wormyrocks/super_otamatone/arduino/otamatone/MenuSystem.cpp

/*
   Copyright (c) 2015, 2016 arduino-menusystem
   Licensed under the MIT license (see LICENSE)
*/

#include "MenuSystem.h"
#include <stdlib.h>


// *********************************************************
// MenuComponent
// *********************************************************

MenuComponent::MenuComponent(const char* name)
  : _name(name),
    _has_focus(false),
    _is_current(false)
{
}

const char* MenuComponent::get_name() const
{
  return _name;
}

void MenuComponent::set_name(const char* name)
{
  _name = name;
}

bool MenuComponent::has_focus() const
{
  return _has_focus;
}

bool MenuComponent::is_current() const
{
  return _is_current;
}

void MenuComponent::set_current(bool is_current)
{
  _is_current = is_current;
}



// *********************************************************
// Menu
// *********************************************************

Menu::Menu(const char* name)
  : MenuComponent(name),
    _p_current_component(nullptr),
    _menu_components(nullptr),
    _p_parent(nullptr),
    _select_fn(nullptr),
    _num_components(0),
    _current_component_num(0),
    _previous_component_num(0)
{
}

bool Menu::next(bool loop)
{
  _previous_component_num = _current_component_num;

  if (!_num_components)
  {
    return false;
  }
  else if (_current_component_num != _num_components - 1)
  {
    _current_component_num++;
    _p_current_component = _menu_components[_current_component_num];

    _p_current_component->set_current();
    _menu_components[_previous_component_num]->set_current(false);
    return true;
  }
  else if (loop)
  {
    _current_component_num = 0;
    _p_current_component = _menu_components[_current_component_num];

    _p_current_component->set_current();
    _menu_components[_previous_component_num]->set_current(false);

    return true;
  }
  return false;
}

bool Menu::prev(bool loop)
{
  _previous_component_num = _current_component_num;

  if (!_num_components)
  {
    return false;
  }
  else if (_current_component_num != 0)
  {
    _current_component_num--;
    _p_current_component = _menu_components[_current_component_num];

    _p_current_component->set_current();
    _menu_components[_previous_component_num]->set_current(false);

    return true;
  }
  else if (loop)
  {
    _current_component_num = _num_components - 1;
    _p_current_component = _menu_components[_current_component_num];

    _p_current_component->set_current();
    _menu_components[_previous_component_num]->set_current(false);

    return true;
  }
  return false;
}

Menu* Menu::activate()
{
  if (!_num_components)
    return nullptr;

  MenuComponent* pComponent = _menu_components[_current_component_num];

  if (pComponent == nullptr)
    return nullptr;

  return pComponent->select();
}

void Menu::set_select_function(SelectFnPtr select_fn)
{
  _select_fn = select_fn;
}

Menu* Menu::select()
{
  return this;
}

void Menu::reset()
{
  for (int i = 0; i < _num_components; ++i)
    _menu_components[i]->reset();

  _p_current_component->set_current(false);
  _previous_component_num = 0;
  _current_component_num = 0;
  _p_current_component = _num_components ? _menu_components[0] : nullptr;
  _p_current_component->set_current();
}

void Menu::add_item(MenuItem* pItem)
{
  // Resize menu component list, keeping existing items.
  // If it fails, there the item is not added and the function returns.
  _menu_components = (MenuComponent**) realloc(_menu_components,
                     (_num_components + 1)
                     * sizeof(MenuComponent*));
  if (_menu_components == nullptr)
    return;

  _menu_components[_num_components] = pItem;

  if (_num_components == 0)
  {
    _p_current_component = pItem;
    _p_current_component->set_current();
  }

  _num_components++;
}

void Menu::hide_n_items(uint8_t n) {
  _num_components -= n;
}

void Menu::show_n_items(uint8_t n) {
  _num_components += n;
}

Menu const* Menu::get_parent() const
{
  return _p_parent;
}

void Menu::set_parent(Menu* pParent)
{
  _p_parent = pParent;
}

void Menu::add_menu(Menu* pMenu)
{
  // Resize menu component list, keeping existing items.
  // If it fails, there the item is not added and the function returns.
  _menu_components = (MenuComponent**) realloc(_menu_components,
                     (_num_components + 1)
                     * sizeof(MenuComponent*));
  if (_menu_components == nullptr)
    return;

  pMenu->set_parent(this);

  _menu_components[_num_components] = pMenu;

  if (_num_components == 0)
  {
    _p_current_component = pMenu;
    _p_current_component->set_current();
  }

  _num_components++;
}

MenuComponent const* Menu::get_menu_component(uint8_t index) const
{
  return _menu_components[index];
}

MenuComponent const* Menu::get_current_component() const
{
  return _p_current_component;
}

uint8_t Menu::get_num_components() const
{
  return _num_components;
}

uint8_t Menu::get_current_component_num() const
{
  return _current_component_num;
}

uint8_t Menu::get_previous_component_num() const
{
  return _previous_component_num;
}

void Menu::render(MenuComponentRenderer const& renderer) const
{
  renderer.render_menu(*this);
}

void Menu::fs_render(MenuComponentRenderer const& renderer) const
{
  renderer.fs_menu_render(*this);
}

// *********************************************************
// BigNumberComponent
// *********************************************************

BigNumberSlider::BigNumberSlider(const char* name,
                                 uint8_t value, uint8_t minValue, uint8_t maxValue,
                                 uint8_t increment, uint8_t animation, SelectFnPtr select_fn)
  : Menu(name),
    _value(value),
    _minValue(minValue),
    _maxValue(maxValue),
    _increment(increment),
    _animation(animation)

{
  set_select_function(select_fn);
  _slider_divs = (maxValue - minValue) / increment;
};

Menu* BigNumberSlider::select()
{
  _has_focus = !_has_focus;
  // Only run _select_fn when the user is done editing the value
  if (!_has_focus && _select_fn != nullptr)
    _select_fn(this);
  return nullptr;
}

void BigNumberSlider::render(MenuComponentRenderer const& renderer) const
{
  renderer.render_big_number_item(*this);
}
void BigNumberSlider::fs_render(MenuComponentRenderer const& renderer) const
{
  renderer.fs_bignumber_render(*this);
}
uint8_t BigNumberSlider::get_value() const
{
  return _value;
}

uint8_t BigNumberSlider::get_minValue() const
{
  return _minValue;
}

uint8_t BigNumberSlider::get_maxValue() const
{
  return _maxValue;
}

void BigNumberSlider::set_value(uint8_t value)
{
  _value = value;
}

void BigNumberSlider::set_min_value(uint8_t value)
{
  _minValue = value;
}

void BigNumberSlider::set_max_value(uint8_t value)
{
  _maxValue = value;
}

bool BigNumberSlider::next(bool loop)
{
  _value += _increment;
  if (_value > _maxValue)
  {
    if (loop)
      _value = _minValue;
    else
      _value = _maxValue;
  }
  return true;
}

bool BigNumberSlider::prev(bool loop)
{
  _value -= _increment;
  if (_value < _minValue)
  {
    if (loop)
      _value = _maxValue;
    else
      _value = _minValue;
  }
  return true;
}

uint8_t BigNumberSlider::get_current_component_num() const
{
  return _value;
}

uint8_t BigNumberSlider::get_num_components() const
{
  return _slider_divs;
}

uint8_t BigNumberSlider::get_animation() const {
  return _animation;
}

// *********************************************************
// BackMenuItem
// *********************************************************

BackMenuItem::BackMenuItem(const char* name, SelectFnPtr select_fn,
                           MenuSystem* ms)
  : MenuItem(name, select_fn),
    menu_system(ms)
{
}

Menu* BackMenuItem::select()
{
  if (_select_fn != nullptr)
    _select_fn(this);

  if (menu_system != nullptr)
    menu_system->back();

  return nullptr;
}

void BackMenuItem::render(MenuComponentRenderer const& renderer) const
{
  renderer.render_back_menu_item(*this);
}

// *********************************************************
// MenuItem
// *********************************************************

MenuItem::MenuItem(const char* name, SelectFnPtr select_fn)
  : MenuComponent(name),
    _select_fn(select_fn)
{
}

void MenuItem::set_select_function(SelectFnPtr select_fn)
{
  _select_fn = select_fn;
}

Menu* MenuItem::select()
{
  if (_select_fn != nullptr)
    _select_fn(this);

  return nullptr;
}

void MenuItem::reset()
{
  // Do nothing.
}

void MenuItem::render(MenuComponentRenderer const& renderer) const
{
  renderer.render_menu_item(*this);
}

bool MenuItem::next(bool loop)
{
  return false;
}

bool MenuItem::prev(bool loop)
{
  return false;
}

// *********************************************************
// NumericMenuItem
// *********************************************************

NumericMenuItem::NumericMenuItem(const char* basename, SelectFnPtr select_fn,
                                 float value, float minValue, float maxValue,
                                 float increment,
                                 FormatValueFnPtr format_value_fn)
  : MenuItem(basename, select_fn),
    _value(value),
    _minValue(minValue),
    _maxValue(maxValue),
    _increment(increment),
    _format_value_fn(format_value_fn)
{
  if (_increment < 0.0) _increment = -_increment;
  if (_minValue > _maxValue)
  {
    float tmp = _maxValue;
    _maxValue = _minValue;
    _minValue = tmp;
  }
};

void NumericMenuItem::set_number_formatter(FormatValueFnPtr format_value_fn)
{
  _format_value_fn = format_value_fn;
}

Menu* NumericMenuItem::select()
{
  _has_focus = !_has_focus;

  // Only run _select_fn when the user is done editing the value
  if (!_has_focus && _select_fn != nullptr)
    _select_fn(this);
  return nullptr;
}

void NumericMenuItem::render(MenuComponentRenderer const& renderer) const
{
  renderer.render_numeric_menu_item(*this);
}

float NumericMenuItem::get_value() const
{
  return _value;
}

float NumericMenuItem::get_minValue() const
{
  return _minValue;
}

float NumericMenuItem::get_maxValue() const
{
  return _maxValue;
}

String NumericMenuItem::get_value_string() const
{
  String buffer;
  if (_format_value_fn != nullptr)
    buffer += _format_value_fn(_value);
  else
    buffer += _value;
  return buffer;
}

void NumericMenuItem::set_value(float value)
{
  _value = value;
}

void NumericMenuItem::set_min_value(float value)
{
  _minValue = value;
}

void NumericMenuItem::set_max_value(float value)
{
  _maxValue = value;
}

bool NumericMenuItem::next(bool loop)
{
  _value += _increment;
  if (_value > _maxValue)
  {
    if (loop)
      _value = _minValue;
    else
      _value = _maxValue;
  }
  return true;
}

bool NumericMenuItem::prev(bool loop)
{
  _value -= _increment;
  if (_value < _minValue)
  {
    if (loop)
      _value = _maxValue;
    else
      _value = _minValue;
  }
  return true;
}


// *********************************************************
// MenuSystem
// *********************************************************

MenuSystem::MenuSystem(MenuComponentRenderer const& renderer)
  : _p_root_menu(new Menu("")),
    _p_curr_menu(_p_root_menu),
    _renderer(renderer)
{
}

bool MenuSystem::next(bool loop)
{
  if (_p_curr_menu->_p_current_component == nullptr) return _p_curr_menu->next(loop);
  if (_p_curr_menu->_p_current_component->has_focus())
    return _p_curr_menu->_p_current_component->next(loop);
  else
    return _p_curr_menu->next(loop);
}

bool MenuSystem::prev(bool loop)
{
  if (_p_curr_menu->_p_current_component == nullptr) return _p_curr_menu->prev(loop);
  if (_p_curr_menu->_p_current_component->has_focus())
    return _p_curr_menu->_p_current_component->prev(loop);
  else
    return _p_curr_menu->prev(loop);
}

void MenuSystem::reset()
{
  _p_curr_menu = _p_root_menu;
  _p_root_menu->reset();
}

void MenuSystem::select(bool reset)
{
  Menu* pMenu = _p_curr_menu->activate();

  if (pMenu != nullptr)
    _p_curr_menu = pMenu;
  else if (reset)
    this->reset();
}

bool MenuSystem::back()
{
  if (_p_curr_menu->_select_fn != nullptr){
    _p_curr_menu->_select_fn(_p_curr_menu);
  }

  if (_p_curr_menu != _p_root_menu)
  {
    _p_curr_menu = const_cast<Menu*>(_p_curr_menu->get_parent());
    return true;
  }
  // We are already in the root menu
  return false;
}

Menu& MenuSystem::get_root_menu() const
{
  return *_p_root_menu;
}

Menu const* MenuSystem::get_current_menu() const
{
  return _p_curr_menu;
}

void MenuSystem::display() const
{
  if (_p_curr_menu != nullptr)
    _renderer.render(*_p_curr_menu);
}
