wormyrocks/super_otamatone/arduino/otamatone/MenuSystem.h

/*
   Copyright (c) 2015, 2016 arduino-menusystem
   Licensed under the MIT license (see LICENSE)
*/

#ifndef MENUSYSTEM_H
#define MENUSYSTEM_H

#if defined(ARDUINO) && ARDUINO >= 100
#include <Arduino.h>
#else
#include <WProgram.h>
#endif

class Menu;
class MenuComponentRenderer;
class MenuSystem;

//! \brief Abstract base class that represents a component in the menu
//!
//! This is the abstract base class for the main components used to build a
//! menu structure: Menu and MenuItem.
//!
//! MenuComponent should not be used as a base class in clients. Instead use
//! either Menu or MenuItem.
//!
//! MenuComponent is the `Component` part of the composite design pattern (see:
//! https://en.wikipedia.org/wiki/Composite_pattern).
//!
//! \see Menu
//! \see MenuItem
class MenuComponent
{
    friend class MenuSystem;
    friend class Menu;
  public:
    //! \brief Construct a MenuComponent
    //! \param[in] name The name of the menu component that is displayed in
    //!                 clients.
    MenuComponent(const char* name);

    //! \brief Set the component's name
    //! \param[in] name The name of the menu component that is displayed in
    //!                 clients.
    void set_name(const char* name);

    //! \brief Gets the component's name
    //! \returns The component's name.
    const char* get_name() const;

    //! \brief Renders the component using the given MenuComponentRenderer
    //!
    //! This is the `accept` method in the visitor design pattern. It should
    //! call the appropriate method on the given MenuComponentRenderer for
    //! rendering this type of component. This method should be called from the
    //! MenuComponent::render method.
    //!
    //! \param[in] renderer The MenuComponentRenderer to use to render this
    //!                     component
    //!
    //! \see MenuComponentRenderer
    virtual void render(MenuComponentRenderer const& renderer) const = 0;
    //! \brief Returns true if this component has focus; false otherwise
    //!
    //! A component has focus when the next and prev functions are able to
    //! change its state rather than navigate the menu structure. It's
    //! primarily used in NumericMenuItem so next and prev change the value
    //! associated with the component.
    //!
    //! Subclasses should set _has_focus to true when this behaviour is desired
    //! and reset it to false when it's no longer required. The usual place to
    //! do this is in the MenuComponent::select method.
    //!
    //! \returns true if this component has focus, false otherwise.
    //!
    //! \see MenuComponent::select
    //! \see NumericMenuComponent
    bool has_focus() const;

    //! \brief Returns true if this is the current component; false otherwise
    //!
    //! This bool registers if the component is the current selected component.
    //!
    //! Subclasses should use set_current() when the component becomes
    //! activated and use set_previous() once the component is no longer the
    //! current component.
    //!
    //! \returns true if this component is the current component, false
    //!          otherwise.
    //! \see MenuComponent::set_current
    bool is_current() const;

  protected:
    //! \brief Processes the next action
    //!
    //! The behaviour of this function can differ depending on whether
    //! MenuComponent::has_focus returns true or false.
    //!
    //! When MenuComponent::has_focus returns true, this method should change
    //! some state in the component; when it returns false, this method should
    //! navigate the menu structure.
    //!
    //! \param[in] loop if true the action should loop around to the beginning
    //!                 for finite ranges; otherwise overflow should be
    //!                 prevented.
    //! \returns true if the component processed the action, false otherwise.
    //!
    //! \see MenuComponent::prev
    //! \see MenuComponent::has_focus
    virtual bool next(bool loop = false) = 0;

    //! \brief Processes the prev action
    //!
    //! The behaviour of this function can differ depending on whether
    //! MenuComponent::has_focus returns true or false.
    //!
    //! When MenuComponent::has_focus returns true, this method should change
    //! some state in the component; when it returns false, this method should
    //! navigate the menu structure.
    //!
    //! \param[in] loop if true the action should loop around to the end
    //!                 for finite ranges; otherwise overflow should be
    //!                 prevented.
    //! \returns true if the component processed the action, false otherwise.
    //!
    //! \see MenuComponent::next
    //! \see MenuComponent::has_focus
    virtual bool prev(bool loop = false) = 0;

    //! \brief Resets the component to its initial state
    virtual void reset() = 0;

    //! \brief Processes the select action
    //!
    //! When a menu component is selected by the client an action may need to
    //! performed.
    //!
    //! If the component supports focus, this method is the recommended place
    //! set _has_focus to true so the MenuComponent::next and
    //! MenuComponent::prev methods can be used to change some state in the
    //! component.
    //!
    //! \returns The Menu instance selected or nullptr. The returned Menu
    //!          instance is used in MenuSystem::activate to set the current
    //!          menu in the MenuSystem.
    //!
    //! \see MenuComponent::has_focus
    //! \see NumericMenuComponent
    virtual Menu* select() = 0;

    //! \brief Set the current state of the component
    //!
    //! \paran is_current true if this component is the current one; false
    //!                   otherwise.
    //! \see is_current
    void set_current(bool is_current = true);

  protected:
    const char* _name;
    bool _has_focus;
    bool _is_current;
};


//! \brief A MenuComponent that calls a callback function when selected.
//!
//! MenuItem represents the `Leaf` in the composite design pattern (see:
//! https://en.wikipedia.org/wiki/Composite_pattern). When a MenuItem is
//! selected, the user-defined MenuItem::_select_fn callback is called.
//!
//! \see MenuComponent
//! \see Menu
class MenuItem : public MenuComponent
{
  public:
    //! \brief Callback for when the MenuItem is selected
    //!
    //! \param menu_item The menu item being selected.
    using SelectFnPtr = void (*)(MenuItem* menu_item);

  public:
    //! \brief Construct a MenuItem
    //! \param[in] name The name of the menu component that is displayed in
    //!                 clients.
    //! \param[in] select_fn The function to call when the MenuItem is
    //!                      selected.
    MenuItem(const char* name, SelectFnPtr select_fn);

    //! \brief Sets the function to call when the MenuItem is selected
    //! \param[in] select_fn The function to call when the MenuItem is
    //!                      selected.
    void set_select_function(SelectFnPtr select_fn);

    //! \copydoc MenuComponent::render
    virtual void render(MenuComponentRenderer const& renderer) const;

  protected:
    //! \copydoc MenuComponent::next
    //!
    //! This method does nothing in MenyItem.
    virtual bool next(bool loop = false);

    //! \copydoc MenuComponent::prev
    //!
    //! This method does nothing in MenuItem.
    virtual bool prev(bool loop = false);

    //! \copydoc MenuComponent::reset
    //!
    //! This method does nothing in MenuItem.
    virtual void reset();

    //! \copydoc MenuComponent:select
    virtual Menu* select();

  protected:
    SelectFnPtr _select_fn;
};

//! \brief A MenuItem that calls MenuSystem::back() when selected.
//! \see MenuItem
class BackMenuItem : public MenuItem
{
  public:
    BackMenuItem(const char* name, SelectFnPtr select_fn, MenuSystem* ms);

    virtual void render(MenuComponentRenderer const& renderer) const;

  protected:
    virtual Menu* select();

  protected:
    MenuSystem* menu_system;
};


class NumericMenuItem : public MenuItem
{
  public:
    //! \brief Callback for formatting the numeric value into a String.
    //!
    //! \param value The value to convert.
    //! \returns The String representation of value.
    using FormatValueFnPtr = const String (*)(const float value);

  public:
    /// Constructor
    ///
    /// @param name The name of the menu item.
    /// @param select_fn The function to call when this MenuItem is selected.
    /// @param value Default value.
    /// @param minValue The minimum value.
    /// @param maxValue The maximum value.
    /// @param increment How much the value should be incremented by.
    /// @param valueFormatter The custom formatter. If nullptr the String float
    ///                       formatter will be used.
    NumericMenuItem(const char* name, SelectFnPtr select_fn,
                    float value, float minValue, float maxValue,
                    float increment = 1.0,
                    FormatValueFnPtr format_value_fn = nullptr);

    /**
       Sets the custom number formatter.

       @param numberFormat the custom formatter. If nullptr the String float
                           formatter will be used (2 decimals)
    */
    void set_number_formatter(FormatValueFnPtr format_value_fn);

    float get_value() const;
    float get_minValue() const;
    float get_maxValue() const;

    // TODO: get_value_string is a poor name. get_formatted_value maybe?
    String get_value_string() const;
    void set_value(float value);
    void set_min_value(float value);
    void set_max_value(float value);

    virtual void render(MenuComponentRenderer const& renderer) const;

  protected:
    virtual bool next(bool loop = false);
    virtual bool prev(bool loop = false);

    virtual Menu* select();

  protected:
    float _value;
    float _minValue;
    float _maxValue;
    float _increment;
    FormatValueFnPtr _format_value_fn;
};


class Menu : public MenuComponent
{
    friend class MenuSystem;
  public:
    using SelectFnPtr = void (*)(Menu *menu);

    Menu(const char* name);

    void add_item(MenuItem* pItem);
    void add_menu(Menu* pMenu);
    void hide_n_items(uint8_t n);
    void show_n_items(uint8_t n);

    MenuComponent const* get_current_component() const;
    MenuComponent const* get_menu_component(uint8_t index) const;

    virtual uint8_t get_num_components() const;
    virtual uint8_t get_current_component_num() const;
    virtual uint8_t get_previous_component_num() const;

    virtual void render(MenuComponentRenderer const& renderer) const;
    virtual void fs_render(MenuComponentRenderer const& renderer) const;
  protected:
    void set_parent(Menu* pParent);
    Menu const* get_parent() const;

    Menu* activate();
    virtual bool next(bool loop = false);
    virtual bool prev(bool loop = false);
    virtual Menu* select();
    virtual void reset();
    void set_select_function(SelectFnPtr select_fn);
    SelectFnPtr _select_fn;

  private:
    MenuComponent* _p_current_component;
    MenuComponent** _menu_components;
    Menu* _p_parent;
    uint8_t _num_components;
    uint8_t _current_component_num;
    uint8_t _previous_component_num;
};

class BigNumberSlider : public Menu
{
  public:

    BigNumberSlider(const char* name,
                    uint8_t value, uint8_t minValue, uint8_t maxValue,
                    uint8_t increment, uint8_t animation, SelectFnPtr select_fn);


    uint8_t get_value() const;
    uint8_t get_minValue() const;
    uint8_t get_maxValue() const;
    uint8_t get_animation() const;
    uint8_t get_num_components() const;
    uint8_t get_current_component_num() const;

    void set_value(uint8_t value);
    void set_min_value(uint8_t value);
    void set_max_value(uint8_t value);
    virtual void render(MenuComponentRenderer const& renderer) const;
    virtual void fs_render(MenuComponentRenderer const& renderer) const;

  protected:
    virtual bool next(bool loop = false);
    virtual bool prev(bool loop = false);
    virtual Menu* select();

  private:
    uint8_t _value;
    uint8_t _animation;
    uint8_t _minValue;
    uint8_t _maxValue;
    uint8_t _increment;
    uint8_t _slider_divs;

};


class MenuSystem
{
  public:
    MenuSystem(MenuComponentRenderer const& renderer);

    void display() const;
    bool next(bool loop = false);
    bool prev(bool loop = false);
    void reset();
    void select(bool reset = false);
    bool back();

    Menu& get_root_menu() const;
    Menu const* get_current_menu() const;

  private:
    Menu* _p_root_menu;
    Menu* _p_curr_menu;
    MenuComponentRenderer const& _renderer;
};


class MenuComponentRenderer
{
  public:
    virtual void render(Menu const& menu) const = 0;
    virtual void render_menu_item(MenuItem const& menu_item) const = 0;
    virtual void render_back_menu_item(BackMenuItem const& menu_item) const = 0;
    virtual void render_numeric_menu_item(NumericMenuItem const& menu_item) const = 0;
    virtual void render_menu(Menu const& menu) const = 0;
    virtual void render_big_number_item(BigNumberSlider const& big_number) const = 0;
    virtual void fs_bignumber_render(BigNumberSlider const& big_number) const = 0;
    virtual void fs_menu_render(Menu const& menu) const = 0;
};


#endif
